brodenn/RoboRacer/omnix/Omni-X_Carrier-Plate.png

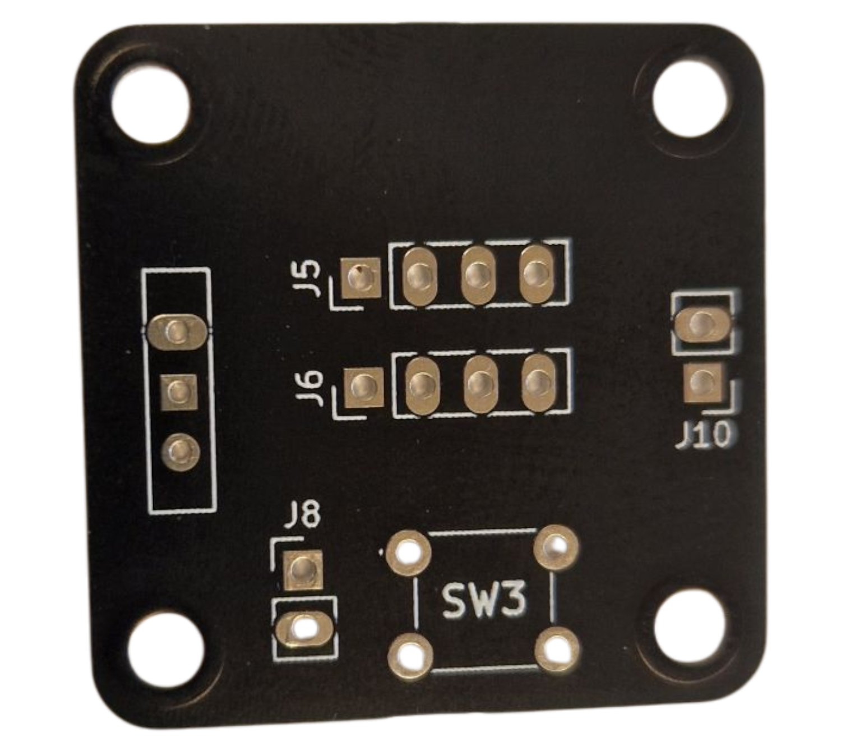
omnix/Omni-X_Carrier-Plate.png
