brodenn/RoboRacer/Panzer/Components/12V_Li-Ion_2200mAh.png

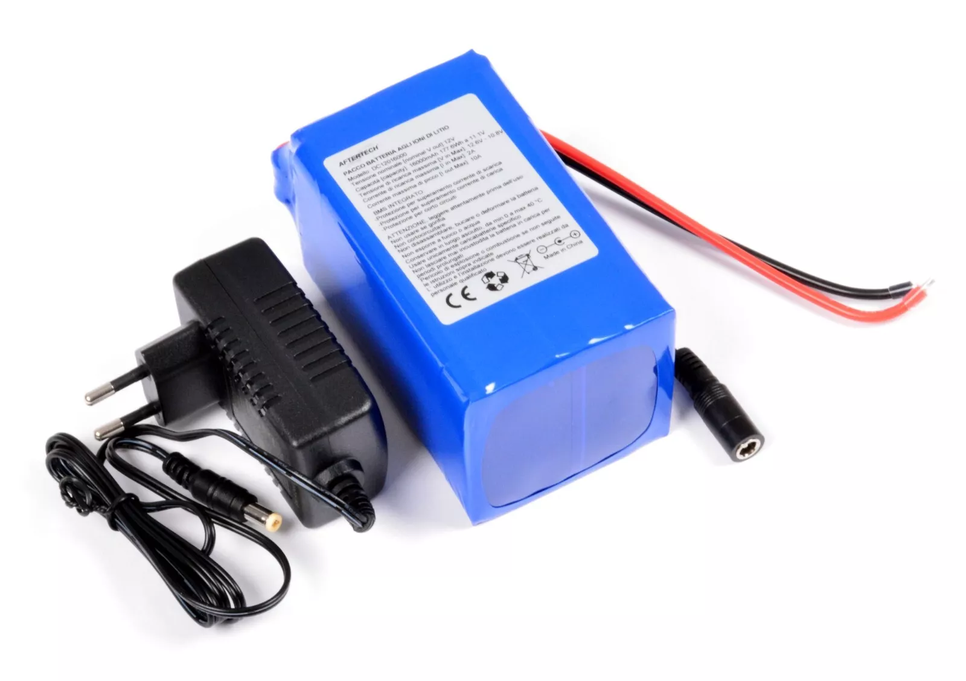
Panzer/Components/12V_Li-Ion_2200mAh.png
