brodenn/RoboRacer/Panzer/Components/12V_Li-Ion_2200mAh.webp

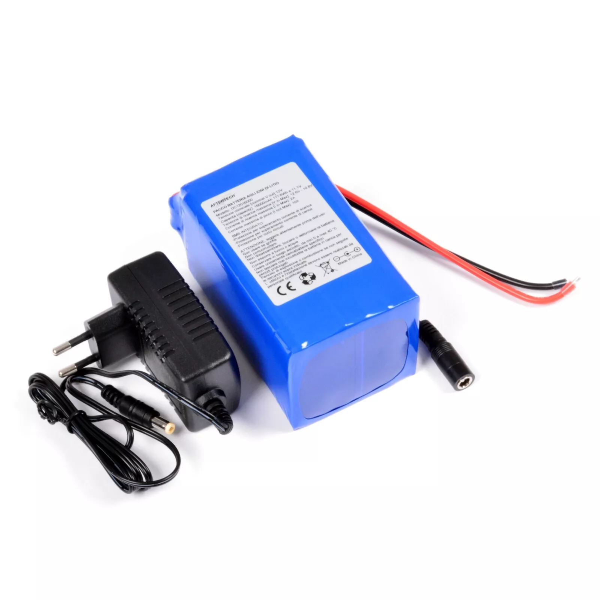
Panzer/Components/12V_Li-Ion_2200mAh.webp
