brodenn/RoboRacer/Panzer/Components/OPT3101.jpeg

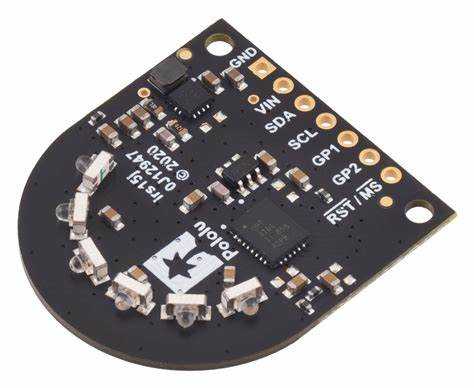
Panzer/Components/OPT3101.jpeg
