brodenn/RoboRacer/Panzer/Components/Panzer_ODT.png

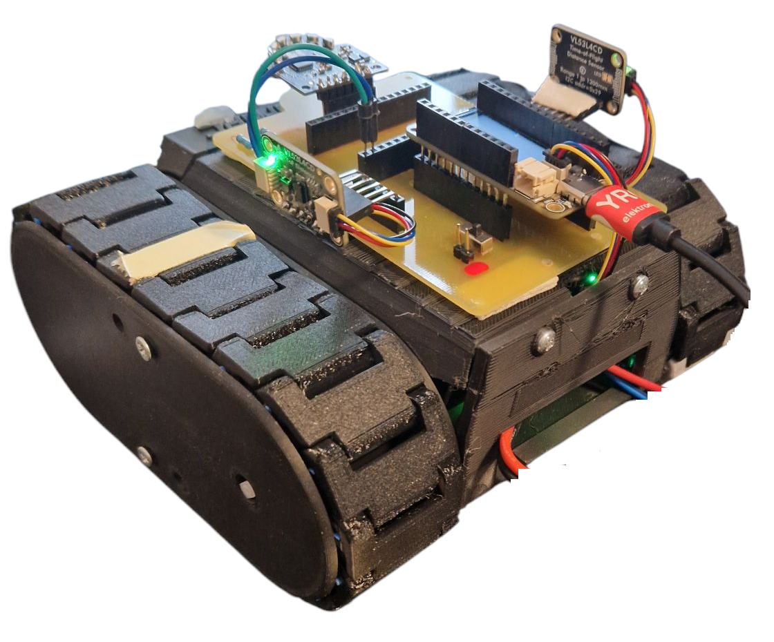
Panzer/Components/Panzer_ODT.png
