brodenn/RoboRacer/Panzer/Components/PCA9546-4CH.jpg

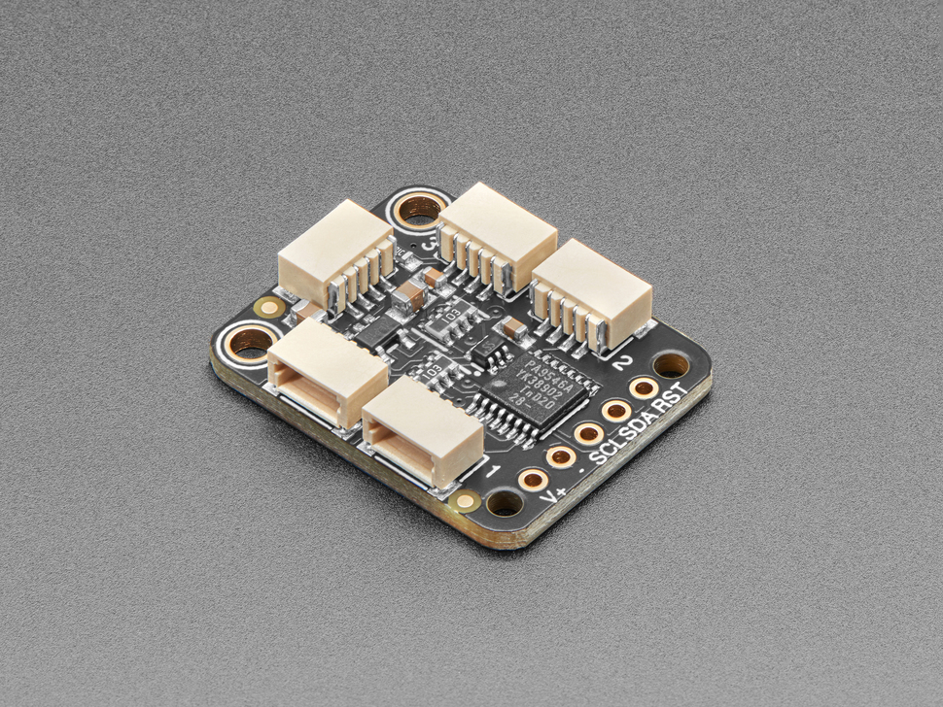
Panzer/Components/PCA9546-4CH.jpg
