brodenn/RoboRacer/Panzer/Panzer_Code/ODT/ODT/secrets.h

#ifndef SECRETS_H
#define SECRETS_H

#define WIFI_SSID     "BatNet-5G-1"
#define WIFI_PASSWORD "slut1jiddr1!"

#define OTA_PASSWORD  "update123"
#define AP_SSID       "Panzer_AP"
#define AP_PASSWORD   "update123"

#endif
